power-analyzer/hardware/Data and Simulations/Voltage Analyzer.asc

C1: cap; 10µ
R1: res; 500k
R2: res; 500k
R3: res; 1.5Meg
R4: res; 1Meg
V1: voltage; SINE(0 10 60)
V2: voltage; 3.3
Named nets: 0, Output
.tran 1 1.2 .2
